PankajaBalasooriya/TrailGuard/Product view/7.pdf

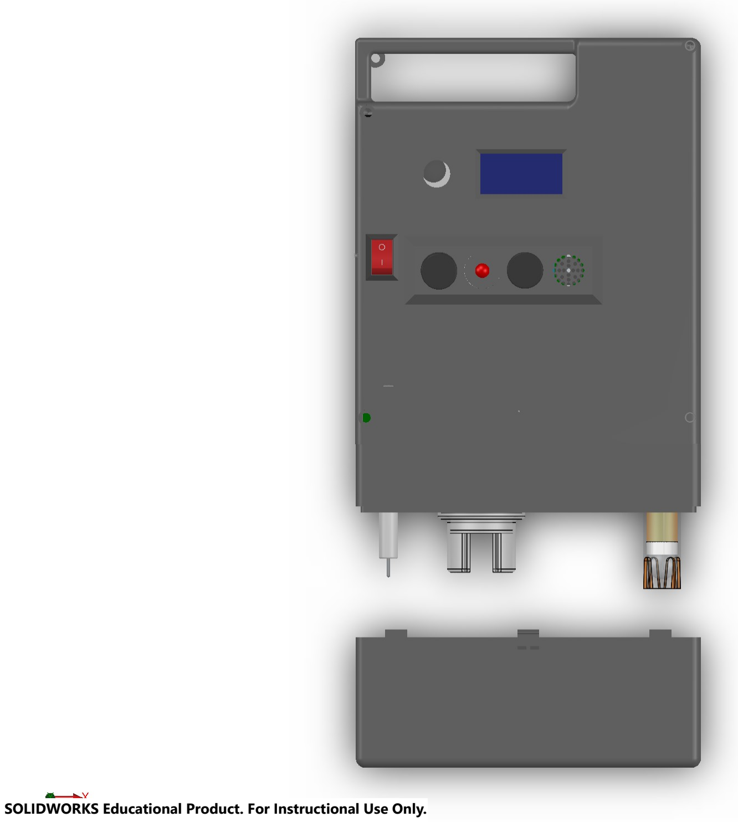
[picture p28: page 1]

SOLIDWORKS Educational Product. For Instructional Use Only.
