PankajaBalasooriya/TrailGuard/Product view/8.pdf

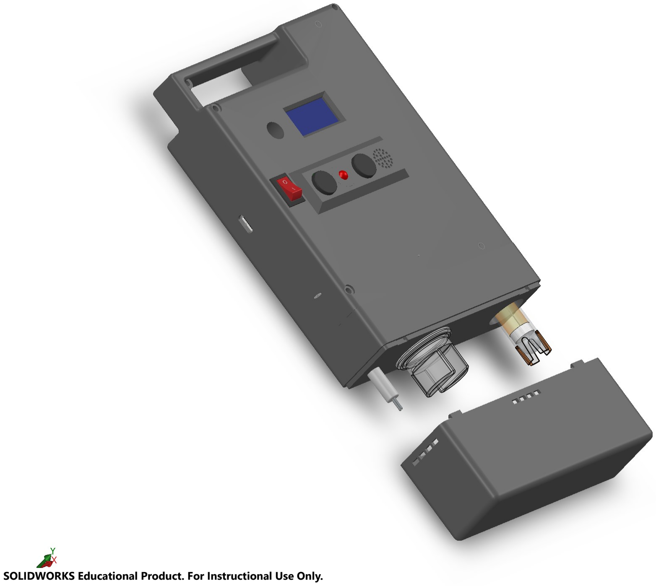
[picture p29: page 1]

SOLIDWORKS Educational Product. For Instructional Use Only.
