PankajaBalasooriya/TrailGuard/documents/Images/7.jpg

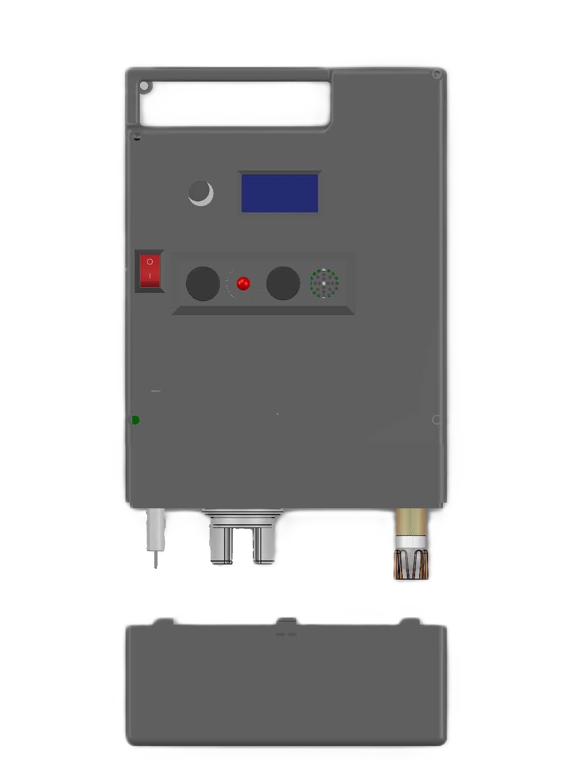
documents/Images/7.jpg
