PankajaBalasooriya/TrailGuard/documents/Images/final.png

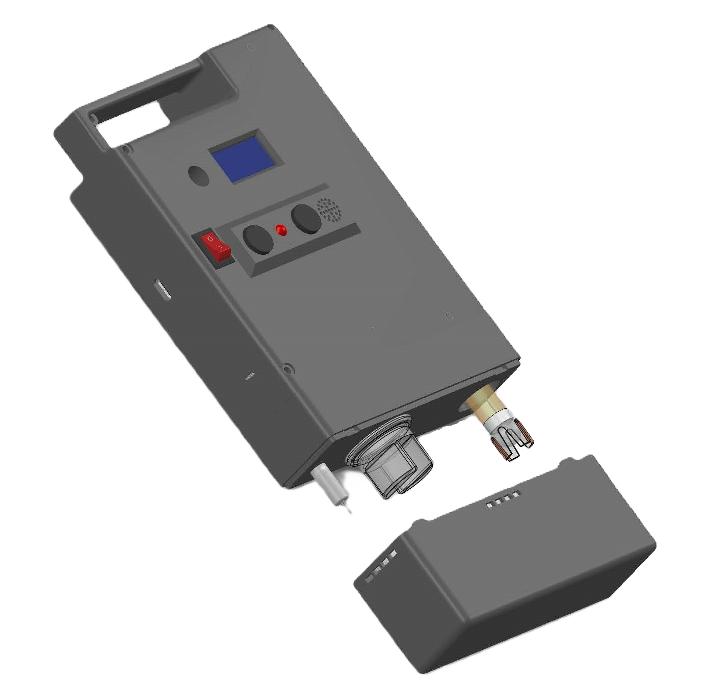
documents/Images/final.png
