PankajaBalasooriya/TrailGuard/documents/Images/finalinternal.png

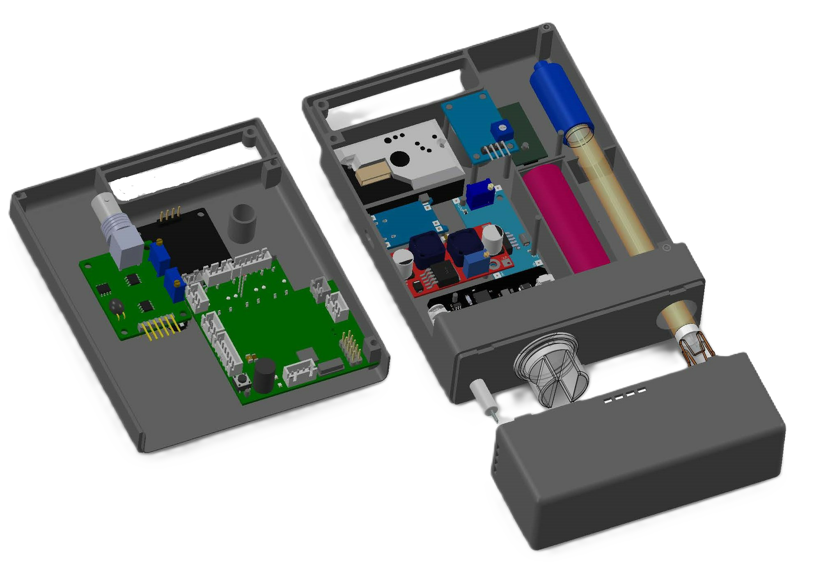
documents/Images/finalinternal.png
