PankajaBalasooriya/TrailGuard/documents/Images/IMG_1129.jpg

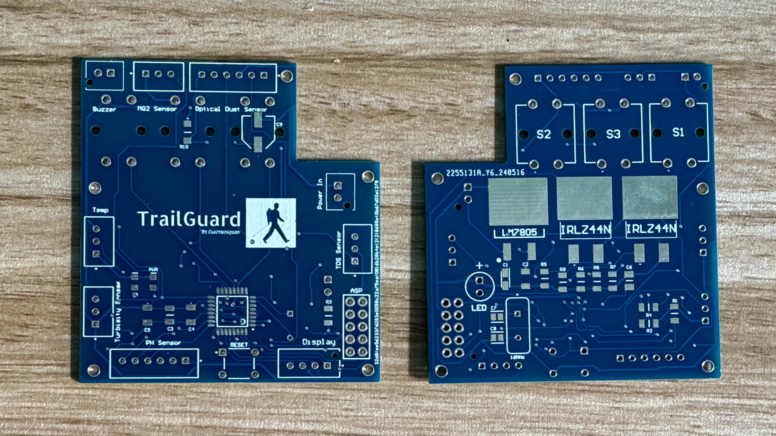
documents/Images/IMG_1129.jpg
