PankajaBalasooriya/TrailGuard/documents/Reference Schematics/WhatsApp Image 2024-04-18 at 11.11.05_b98d9de4.jpg

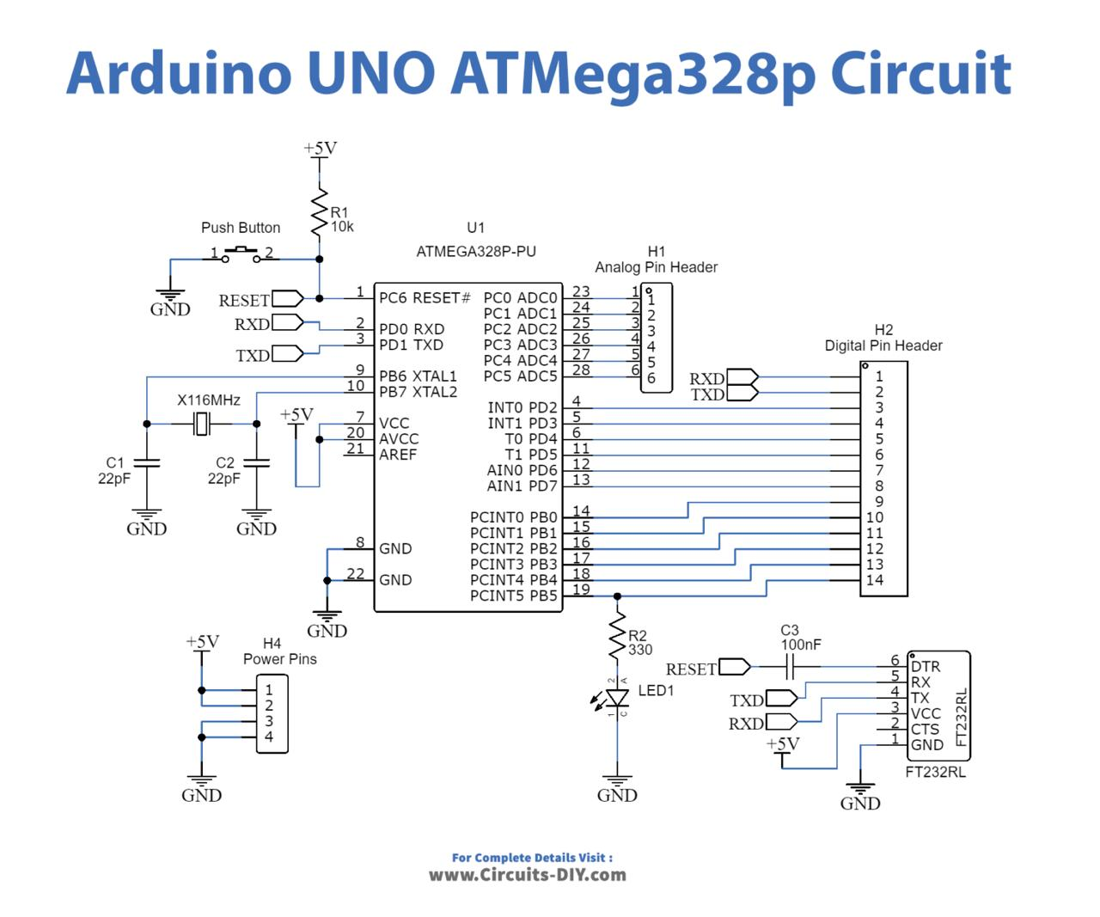
documents/Reference Schematics/WhatsApp Image 2024-04-18 at 11.11.05_b98d9de4.jpg
