PankajaBalasooriya/TrailGuard/Research/WHO-fourth-edition-and-SLS-standards-for-drinking-water.png

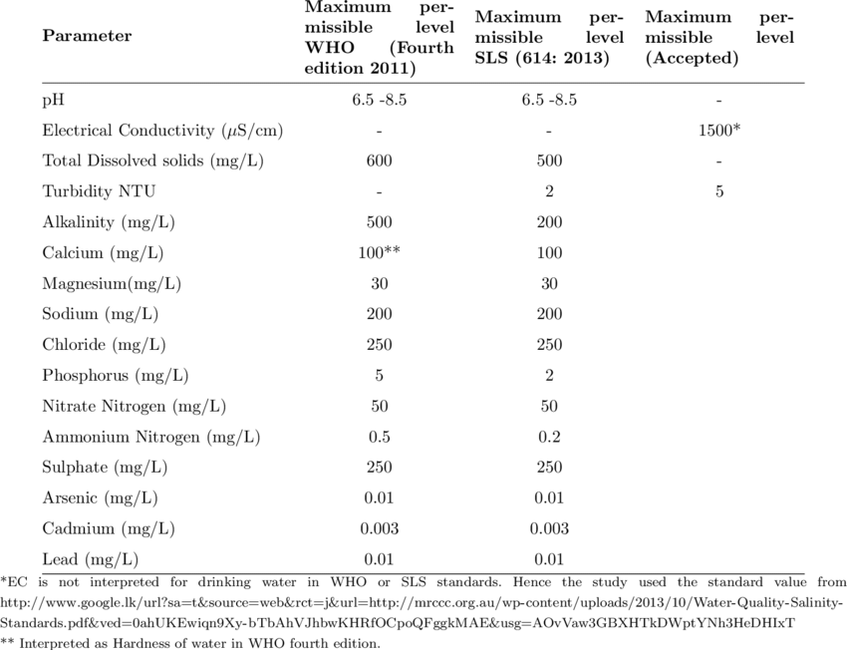
Research/WHO-fourth-edition-and-SLS-standards-for-drinking-water.png
