PankajaBalasooriya/TrailGuard/TrailGuard2.0/PCB/Screenshot 2024-06-17 232150.png

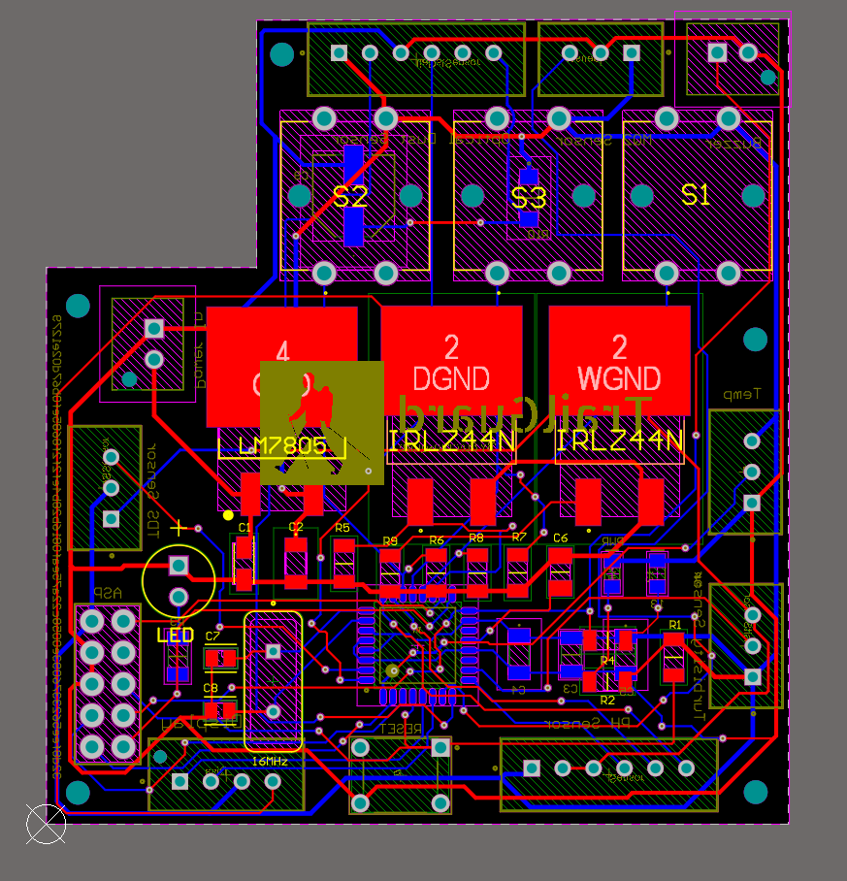
TrailGuard2.0/PCB/Screenshot 2024-06-17 232150.png
