PankajaBalasooriya/TrailGuard/documents/Reference Schematics/MT3608-Step-Up-Power-Module-Dimensions.png

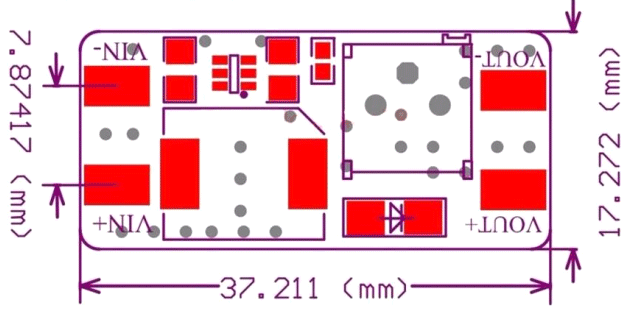
documents/Reference Schematics/MT3608-Step-Up-Power-Module-Dimensions.png
