PankajaBalasooriya/TrailGuard/TrailGuard2.0/TrailGuard2.0.pdf

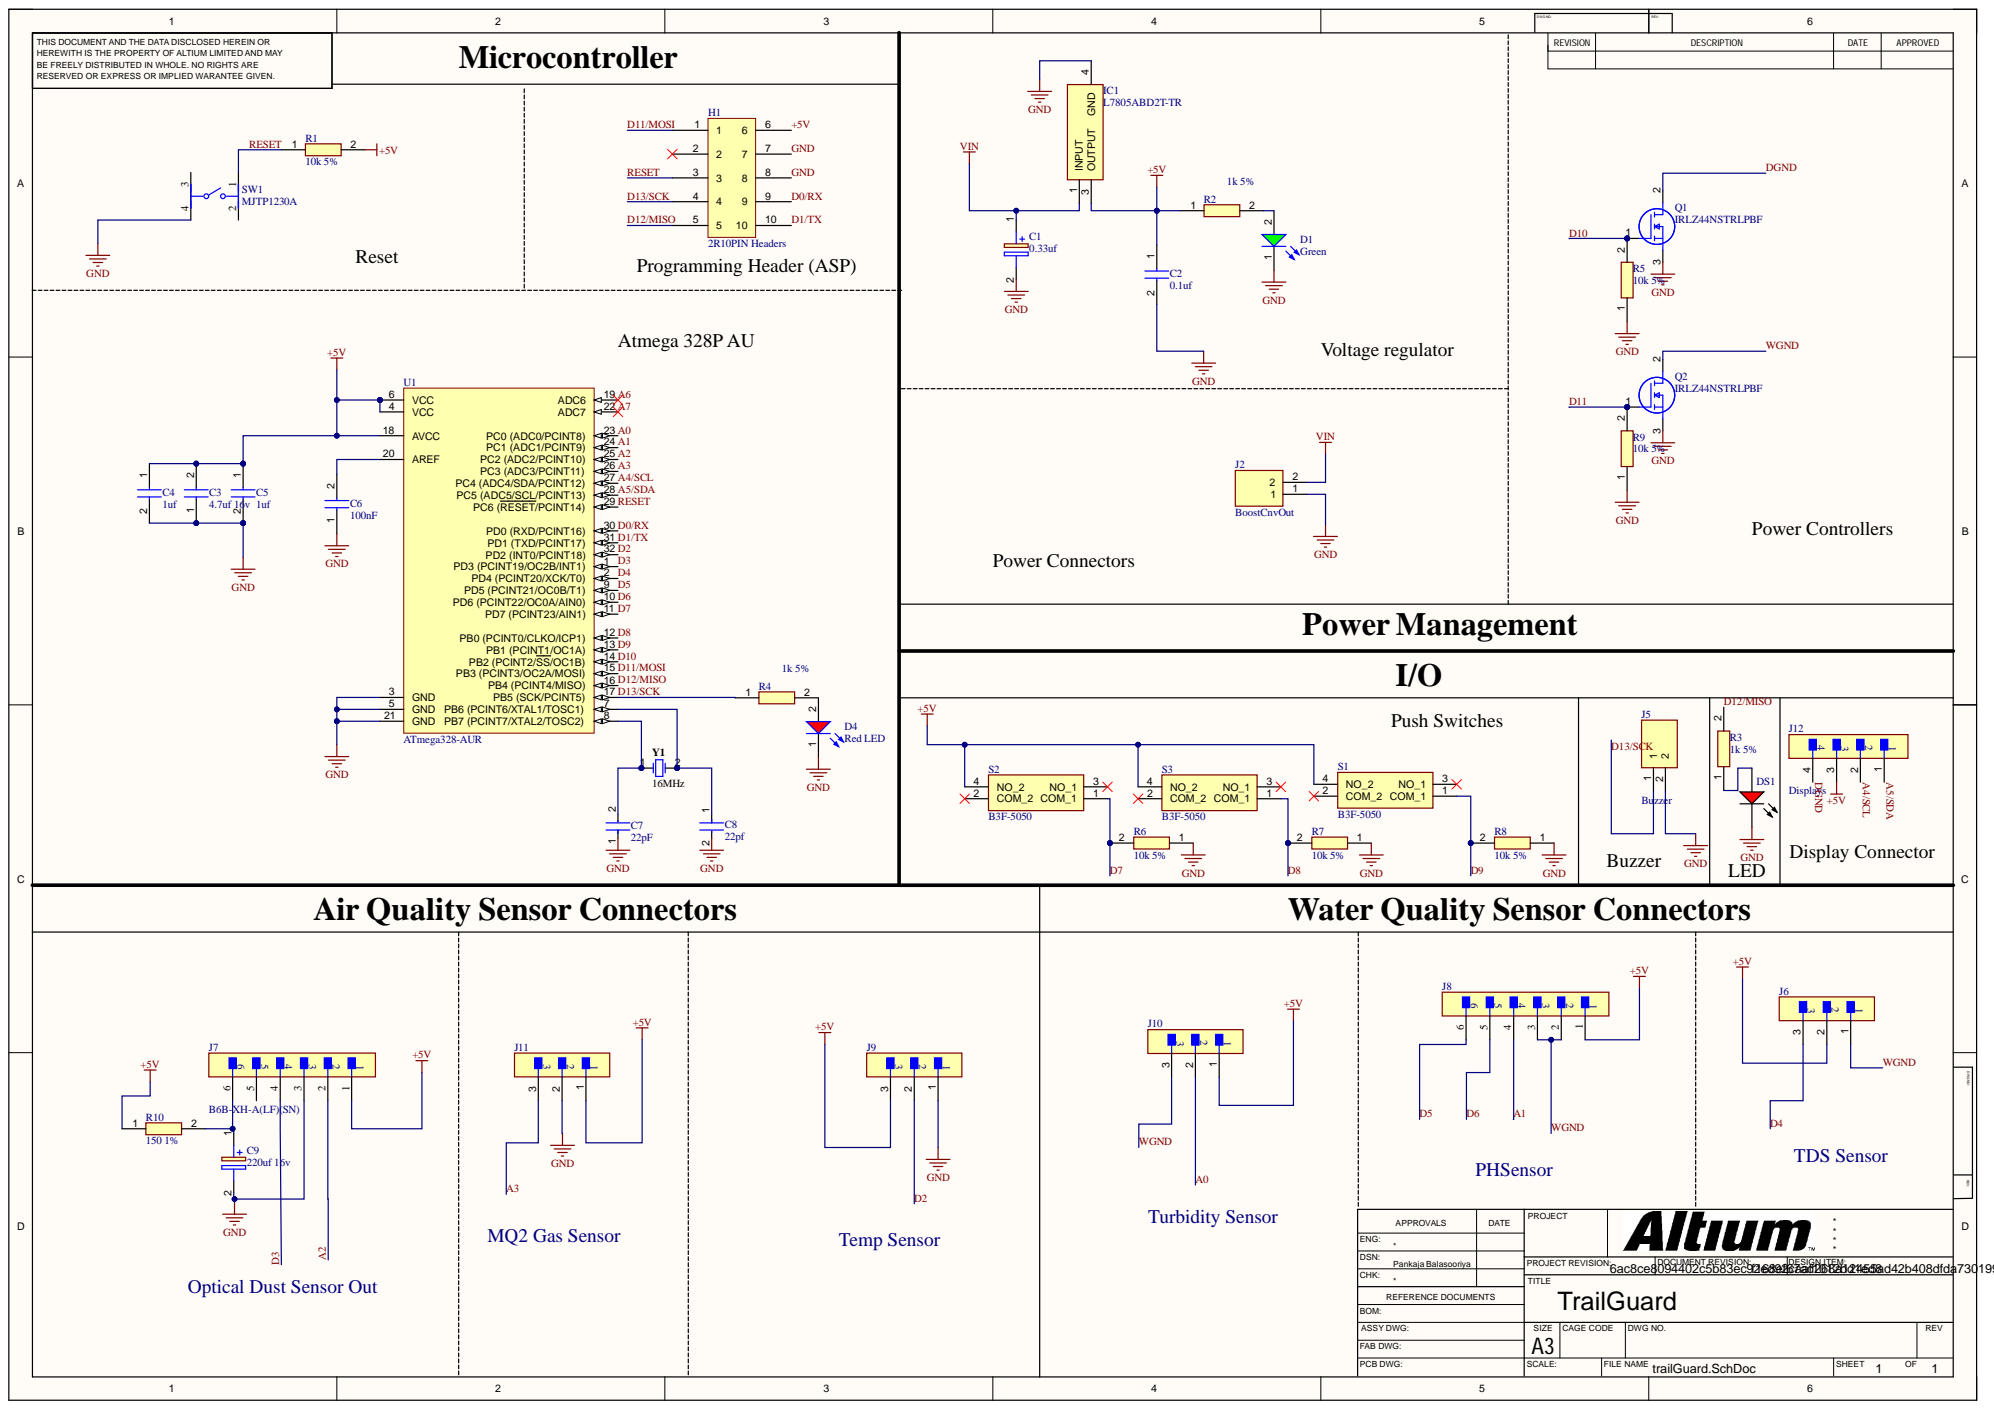
[picture p56: page 1]

THIS DOCUM ENT AND THE DA TA DISCLOS ED HEREIN OR HERE WITH IS THE PROP E RTY OF A LTIUM LIMITED AND M AY B E FRE E LY DISTRIBUTED IN WHOL E. NO RIGHTS ARE RE S E R V ED OR E X PRE S S OR IM P LIED W ARANTE E GIV EN. | Microcontrolle r | REVISION | DESC RIPTION | DAT E | APPROVED

Programming Header (ASP) Reset

1 8 | | 2 3
2 0 | | 2 4

Air Quality Sensor Connectors | Water Quality Sensor Connectors

A P PROV A L S | DATE | PROJECT | ****
CHK : | | : 6ac8ce8094402c5b83ec92ed92caaf1012bd1ed8 f168ef67ad268a12455ad42b408dfda73019952b 1 TITL E TrailGuard

ENG: *P

DSN: a nka j a B alaso o riya | | PROJECT RE VISION: | DOCUM ENT RE VISION: | DE SIGN ITE M

Optical Dust Sensor Out

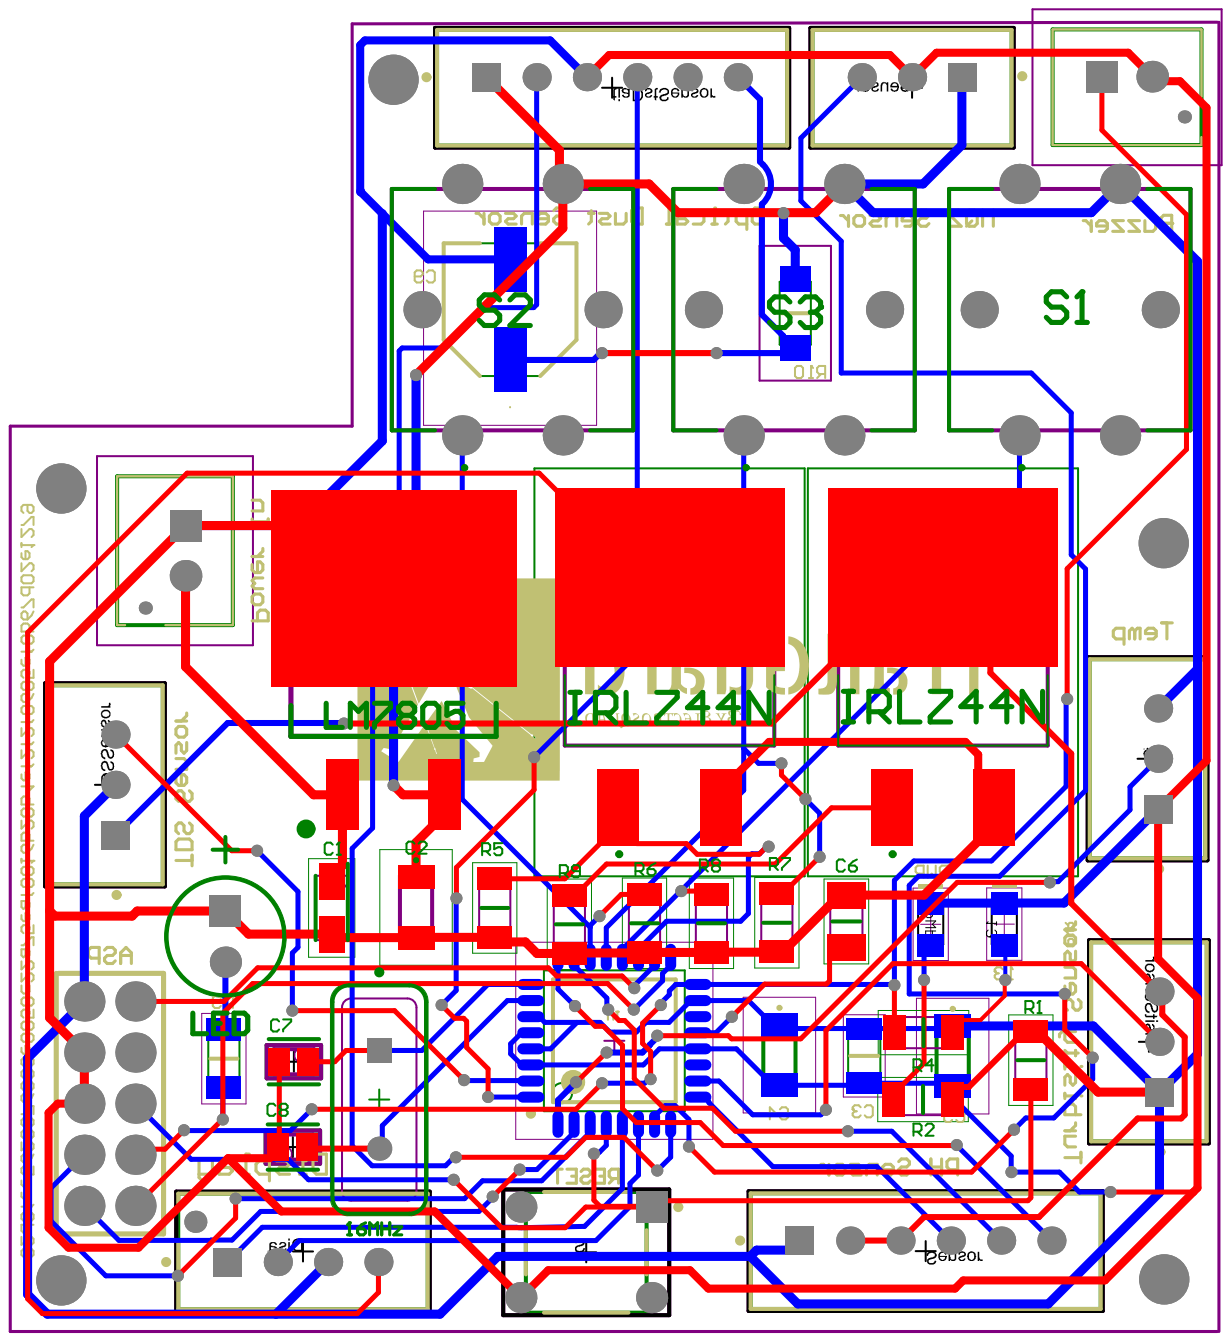
[picture p57: page 2]
