PankajaBalasooriya/TrailGuard/trailguard_code/TDS.cpp

#include "TDS.h"
#include <Arduino.h>

#define VREF 5.0              // analog reference voltage(Volt) of the ADC
#define SCOUNT  30            // sum of sample points

int analogBuffer[SCOUNT];     // store the analog value in the array, read from ADC
int analogBufferTemp[SCOUNT];
int analogBufferIndex = 0;

float averageVoltage = 0;
float tdsValue = 0;

// median filtering algorithm
int getMedianNum(int bArray[], int iFilterLen) {
    int bTab[iFilterLen];
    for (byte i = 0; i < iFilterLen; i++) {
        bTab[i] = bArray[i];
    }
    int i, j, bTemp;
    for (j = 0; j < iFilterLen - 1; j++) {
        for (i = 0; i < iFilterLen - j - 1; i++) {
            if (bTab[i] > bTab[i + 1]) {
                bTemp = bTab[i];
                bTab[i] = bTab[i + 1];
                bTab[i + 1] = bTemp;
            }
        }
    }
    if ((iFilterLen & 1) > 0) {
        bTemp = bTab[(iFilterLen - 1) / 2];
    } else {
        bTemp = (bTab[iFilterLen / 2] + bTab[iFilterLen / 2 - 1]) / 2;
    }
    return bTemp;
}

double tds_value(int tds_pin) {
    static unsigned long analogSampleTimepoint = millis();
    if (millis() - analogSampleTimepoint > 40U) {     // every 40 milliseconds, read the analog value from the ADC
        analogSampleTimepoint = millis();
        analogBuffer[analogBufferIndex] = analogRead(tds_pin);    // read the analog value and store into the buffer
        analogBufferIndex++;
        if (analogBufferIndex == SCOUNT) {
            analogBufferIndex = 0;
        }
    }

    static unsigned long printTimepoint = millis();
    if (millis() - printTimepoint > 800U) {
        printTimepoint = millis();
        for (int copyIndex = 0; copyIndex < SCOUNT; copyIndex++) {
            analogBufferTemp[copyIndex] = analogBuffer[copyIndex];
        }

        // read the analog value more stable by the median filtering algorithm, and convert to voltage value
        averageVoltage = getMedianNum(analogBufferTemp, SCOUNT) * (float)VREF / 1024.0;

        // convert voltage value to tds value
        tdsValue = (133.42 * averageVoltage * averageVoltage * averageVoltage
                    - 255.86 * averageVoltage * averageVoltage
                    + 857.39 * averageVoltage) * 0.5;

    }
    return tdsValue; // Return the last known TDS value if not updating
}
